bioluminesceme/peregrine/images/fusion-sketch-peregrine.png

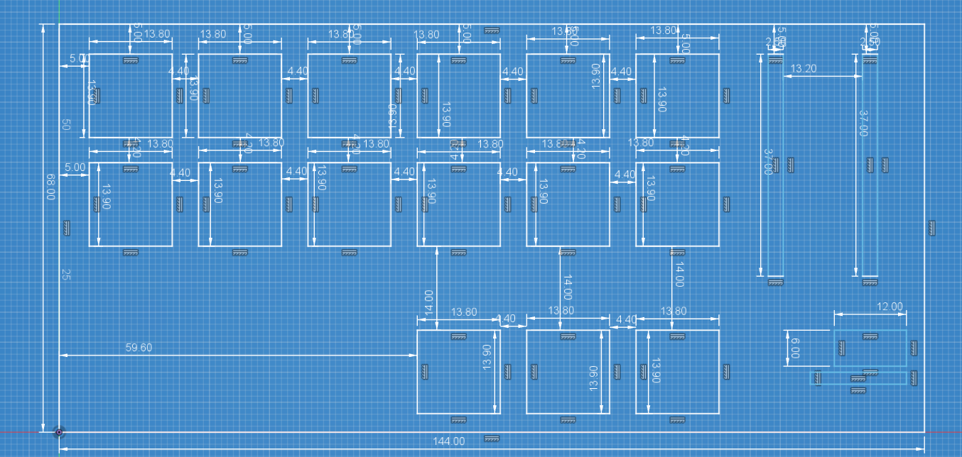
images/fusion-sketch-peregrine.png
