bioluminesceme/peregrine/images/jlc1.png

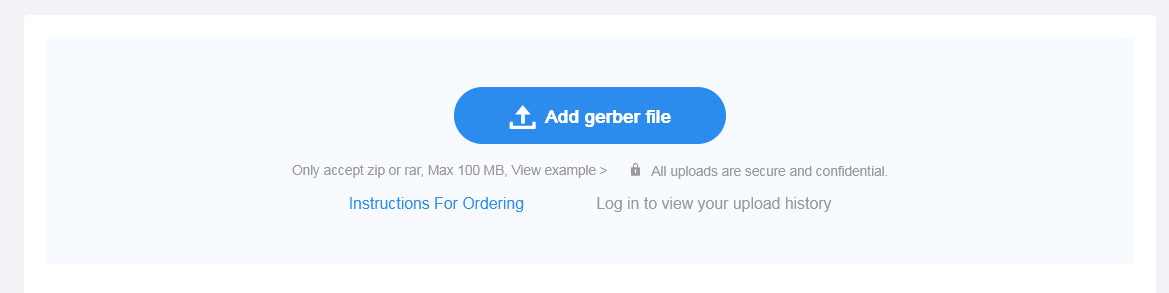
images/jlc1.png
