bioluminesceme/peregrine/images/jlc4.png

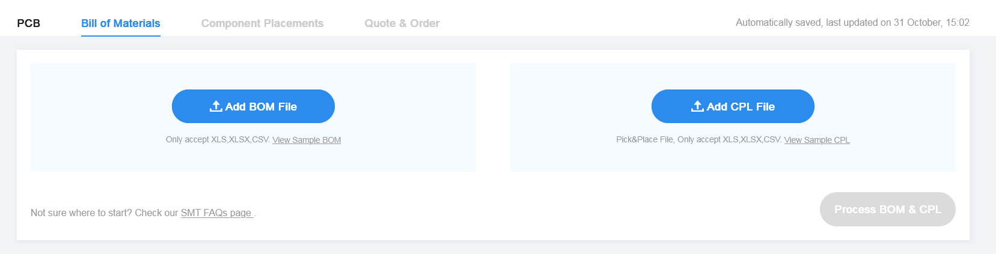
images/jlc4.png
